Shu-YuL/AED-Smart-Alarm/Firmware/Base_Station/main/HD44780.c

#include <driver/i2c.h>
#include <esp_log.h>
#include <freertos/FreeRTOS.h>
#include <freertos/task.h>
#include <stdio.h>
#include "sdkconfig.h"
#include "rom/ets_sys.h"
#include <esp_log.h>
#include <string.h>

// LCD module defines
#define LCD_LINEONE             0x00        // start of line 1
#define LCD_LINETWO             0x40        // start of line 2
#define LCD_LINETHREE           0x14        // start of line 3
#define LCD_LINEFOUR            0x54        // start of line 4

#define LCD_BACKLIGHT           0x08
#define LCD_ENABLE              0x04               
#define LCD_COMMAND             0x00
#define LCD_WRITE               0x01

#define LCD_SET_DDRAM_ADDR      0x80
#define LCD_READ_BF             0x40

// LCD instructions
#define LCD_CLEAR               0x01        // replace all characters with ASCII 'space'
#define LCD_HOME                0x02        // return cursor to first position on first line
#define LCD_ENTRY_MODE          0x06        // shift cursor from left to right on read/write
#define LCD_DISPLAY_OFF         0x08        // turn display off
#define LCD_DISPLAY_ON          0x0C        // display on, cursor off, don't blink character
#define LCD_FUNCTION_RESET      0x30        // reset the LCD
#define LCD_FUNCTION_SET_4BIT   0x28        // 4-bit data, 2-line display, 5 x 7 font
#define LCD_SET_CURSOR          0x80        // set cursor position

// Pin mappings
// P0 -> RS
// P1 -> RW
// P2 -> E
// P3 -> Backlight
// P4 -> D4
// P5 -> D5
// P6 -> D6
// P7 -> D7

static char tag[] = "LCD Driver";
static uint8_t LCD_addr;
static uint8_t SDA_pin;
static uint8_t SCL_pin;
static uint8_t LCD_cols;
static uint8_t LCD_rows;

static void LCD_writeNibble(uint8_t nibble, uint8_t mode);
static void LCD_writeByte(uint8_t data, uint8_t mode);
static void LCD_pulseEnable(uint8_t nibble);


/*------------------------------------------
Function Name: I2C_init()
Description: Intiializes I2C on the the desired pins given by the macros SDA_pin, SCL_pin.
Input: N/A
Output: error code of type esp_err_t
Variables Affected: N/A
-------------------------------------------*/
static esp_err_t I2C_init(void)
{
    i2c_config_t conf = {
        .mode = I2C_MODE_MASTER,
        .sda_io_num = SDA_pin,
        .scl_io_num = SCL_pin,
        .sda_pullup_en = GPIO_PULLUP_ENABLE,
        .scl_pullup_en = GPIO_PULLUP_ENABLE,
        .master.clk_speed = 100000
    };
	i2c_param_config(I2C_NUM_0, &conf);
	i2c_driver_install(I2C_NUM_0, I2C_MODE_MASTER, 0, 0, 0);
    return ESP_OK;
}


/*------------------------------------------
Function Name: LCD_init()
Description: Initializes the LCD screen, clears the screen and setups the LCD to begin printing. 
Inputs: addr, dataPin, clockPin, cols, rows
Output: N/A
Variables Affected: N/A
-------------------------------------------*/
void LCD_init(uint8_t addr, uint8_t dataPin, uint8_t clockPin, uint8_t cols, uint8_t rows)
{
    LCD_addr = addr;
    SDA_pin = dataPin;
    SCL_pin = clockPin;
    LCD_cols = cols;
    LCD_rows = rows;
    I2C_init();
    vTaskDelay(100 / portTICK_PERIOD_MS);                                 // Initial 40 mSec delay

    // Reset the LCD controller
    LCD_writeNibble(LCD_FUNCTION_RESET, LCD_COMMAND);                   // First part of reset sequence
    vTaskDelay(10 / portTICK_PERIOD_MS);                                  // 4.1 mS delay (min)
    LCD_writeNibble(LCD_FUNCTION_RESET, LCD_COMMAND);                   // second part of reset sequence
    ets_delay_us(200);                                                  // 100 uS delay (min)
    LCD_writeNibble(LCD_FUNCTION_RESET, LCD_COMMAND);                   // Third time's a charm
    LCD_writeNibble(LCD_FUNCTION_SET_4BIT, LCD_COMMAND);                // Activate 4-bit mode
    ets_delay_us(80);                                                   // 40 uS delay (min)

    // --- Busy flag now available ---
    // Function Set instruction
    LCD_writeByte(LCD_FUNCTION_SET_4BIT, LCD_COMMAND);                  // Set mode, lines, and font
    ets_delay_us(80); 

    // Clear Display instruction
    LCD_writeByte(LCD_CLEAR, LCD_COMMAND);                              // clear display RAM
    vTaskDelay(2 / portTICK_PERIOD_MS);                                   // Clearing memory takes a bit longer
    
    // Entry Mode Set instruction
    LCD_writeByte(LCD_ENTRY_MODE, LCD_COMMAND);                         // Set desired shift characteristics
    ets_delay_us(80); 

    LCD_writeByte(LCD_DISPLAY_ON, LCD_COMMAND);                         // Ensure LCD is set to on
}


/*------------------------------------------
Function Name: LCD_setCursor()
Description: Moves the cursor to the location (row,col) specified by the inputs row and col. 
             Call this function to print a character at a desired location.
Inputs: col, row
Output: N/A
Variables Affected: N/A
-------------------------------------------*/
void LCD_setCursor(uint8_t col, uint8_t row)
{
    if (row > LCD_rows - 1) {
        ESP_LOGE(tag, "Cannot write to row %d. Please select a row in the range (0, %d)", row, LCD_rows-1);
        row = LCD_rows - 1;
    }
    uint8_t row_offsets[] = {LCD_LINEONE, LCD_LINETWO, LCD_LINETHREE, LCD_LINEFOUR};
    LCD_writeByte(LCD_SET_DDRAM_ADDR | (col + row_offsets[row]), LCD_COMMAND);
}


/*------------------------------------------
Function Name: LCD_writeChar()
Description: Prints a single character on the LCD screen.
Input: c => ASCII character to print
Output: N/A
Variables Affected: N/A
-------------------------------------------*/
void LCD_writeChar(char c)
{
    LCD_writeByte(c, LCD_WRITE); // Write data to DDRAM
}


/*------------------------------------------
Function Name: LCD_writeStr()
Description: Prints a string of characters on the LCD screen.
Input: str => pointer to string to print.
Output: N/A
Variables Affected: N/A
-------------------------------------------*/
void LCD_writeStr(char* str)
{
    while (*str) {
        LCD_writeChar(*str++);
    }
}


/*------------------------------------------
Function Name: LCD_home()
Description: 
Input: N/A
Output: N/A
Variables Affected: N/A
-------------------------------------------*/
void LCD_home(void)
{
    LCD_writeByte(LCD_HOME, LCD_COMMAND);
    vTaskDelay(2 / portTICK_PERIOD_MS);   // This command takes a while to complete
}


/*------------------------------------------
Function Name: LCD_clearScreen()
Description: Completely clears the LCD screen. Waits 2s to allow screen to finish clearing.
Input: N/A
Output: N/A
Variables Affected: N/A
-------------------------------------------*/
void LCD_clearScreen(void)
{
    LCD_writeByte(LCD_CLEAR, LCD_COMMAND);
    vTaskDelay(2 / portTICK_PERIOD_MS);   // This command takes a while to complete
}


/*------------------------------------------
Function Name: LCD_writeNibble()
Description: Writes a nibble of data to the LCD controller via I2C.
Inputs: nibble => nibble of data to write to LCD
       mode
Output: N/A
Variables Affected: N/A
-------------------------------------------*/
static void LCD_writeNibble(uint8_t nibble, uint8_t mode)
{
    uint8_t data = (nibble & 0xF0) | mode | LCD_BACKLIGHT;
    i2c_cmd_handle_t cmd = i2c_cmd_link_create();
    ESP_ERROR_CHECK(i2c_master_start(cmd));
    ESP_ERROR_CHECK(i2c_master_write_byte(cmd, (LCD_addr << 1) | I2C_MASTER_WRITE, 1));
    ESP_ERROR_CHECK(i2c_master_write_byte(cmd, data, 1));
    ESP_ERROR_CHECK(i2c_master_stop(cmd));
    ESP_ERROR_CHECK(i2c_master_cmd_begin(I2C_NUM_0, cmd, 1000/portTICK_PERIOD_MS));
    i2c_cmd_link_delete(cmd);   

    LCD_pulseEnable(data); // Clock data into LCD
}


/*------------------------------------------
Function Name: LCD_writeByte()
Description: Writes a full byte of data to the LCD controller by writing the upper and lower nibble of data 
             as two transactions using LCD_writeNibble().
Inputs: data => byte of data to write to LCD
        mode
Output: N/A
Variables Affected: N/A
-------------------------------------------*/
static void LCD_writeByte(uint8_t data, uint8_t mode)
{
    LCD_writeNibble(data & 0xF0, mode);
    LCD_writeNibble((data << 4) & 0xF0, mode);
}


/*------------------------------------------
Function Name: LCD_pulseEnable()
Description: 
Input: data
Output: N/A
Variables Affected: N/A
-------------------------------------------*/
static void LCD_pulseEnable(uint8_t data)
{
    i2c_cmd_handle_t cmd = i2c_cmd_link_create();
    ESP_ERROR_CHECK(i2c_master_start(cmd));
    ESP_ERROR_CHECK(i2c_master_write_byte(cmd, (LCD_addr << 1) | I2C_MASTER_WRITE, 1));
    ESP_ERROR_CHECK(i2c_master_write_byte(cmd, data | LCD_ENABLE, 1));
    ESP_ERROR_CHECK(i2c_master_stop(cmd));
    ESP_ERROR_CHECK(i2c_master_cmd_begin(I2C_NUM_0, cmd, 1000/portTICK_PERIOD_MS));
    i2c_cmd_link_delete(cmd);  
    ets_delay_us(1);

    cmd = i2c_cmd_link_create();
    ESP_ERROR_CHECK(i2c_master_start(cmd));
    ESP_ERROR_CHECK(i2c_master_write_byte(cmd, (LCD_addr << 1) | I2C_MASTER_WRITE, 1));
    ESP_ERROR_CHECK(i2c_master_write_byte(cmd, (data & ~LCD_ENABLE), 1));
    ESP_ERROR_CHECK(i2c_master_stop(cmd));
    ESP_ERROR_CHECK(i2c_master_cmd_begin(I2C_NUM_0, cmd, 1000/portTICK_PERIOD_MS));
    i2c_cmd_link_delete(cmd);
    ets_delay_us(500);
}


/*------------------------------------------
Function Name: ()
Description: This function will print any characters to the LCD display. The first argument is the x position,
             the second argument is the y position, the third argument is whatever you wanna write to the OLED display,
             the fourth argument is an integer (if no integer -> write NA), the last argument is a string of characters
             (if no string -> write NA). Please include " " for the third argument.
Inputs: x_position, y_position, txt, var, message
Output: N/A
Variables Affected: N/A
-------------------------------------------*/
void LCD_printf(uint8_t x_position, uint8_t y_position, char txt[], uint8_t var, char message[])
{
    char txtBuf[8];
    uint8_t num_buff;
    if(var)
    {
        LCD_setCursor(y_position, x_position);
        LCD_writeStr(txt);
        num_buff = strlen(txt);
        sprintf(txtBuf, "%d", var);
        LCD_setCursor(++num_buff, x_position);
        LCD_writeStr(txtBuf);
    }
    else if(message)
    {
        LCD_setCursor(y_position, x_position);
        LCD_writeStr(txt);
        num_buff = strlen(txt);
        LCD_setCursor(++num_buff, x_position);
        LCD_writeStr(message);
    }
    else
    {
        LCD_setCursor(y_position, x_position);
        LCD_writeStr(txt);
    }
}
