Shu-YuL/AED-Smart-Alarm/Firmware/Monitoring_Device/main/wifi_functions.c

#include "wifi_include.h"

static const char *TAG = "WIFI";

/* Description: This file contains functions specifically for establishing a WiFi connection to a standard, non-WPA2 WiFi network like DevNet or a home network*/

#ifdef HOME

/* FreeRTOS event group to signal when wifi is connected*/
static EventGroupHandle_t s_wifi_event_group;

static int s_retry_num = 0;

/*------------------------------------------
Function Name: event_handler()
Description: FreeRTOS event handler to indicate when WiFi is connected. 
             Retries to connect to a WiFi access point upto WIFI_MAX_TRIES, and prints IP address of network when successful.
Input: arg, event_base, event_id, event_data
Output: N/A
Variables Affected: s_retry_num, s_wifi_event_group
-------------------------------------------*/
static void event_handler(void *arg, esp_event_base_t event_base,
                          int32_t event_id, void *event_data)
{
    if (event_base == WIFI_EVENT && event_id == WIFI_EVENT_STA_START)
    {
        esp_wifi_connect();
    }
    else if (event_base == WIFI_EVENT && event_id == WIFI_EVENT_STA_DISCONNECTED)
    {
        if (s_retry_num < WIFI_MAX_TRIES)
        {
            esp_wifi_connect();
            s_retry_num++;
            ESP_LOGI(TAG, "retry to connect to the AP");
        }
        else
        {
            xEventGroupSetBits(s_wifi_event_group, WIFI_FAIL_BIT);
        }
        ESP_LOGI(TAG, "connect to the AP fail");
    }
    else if (event_base == IP_EVENT && event_id == IP_EVENT_STA_GOT_IP)
    {
        ip_event_got_ip_t *event = (ip_event_got_ip_t *)event_data;
        ESP_LOGI(TAG, "got ip:" IPSTR, IP2STR(&event->ip_info.ip));
        s_retry_num = 0;
        xEventGroupSetBits(s_wifi_event_group, WIFI_CONNECTED_BIT);
    }
}

/*------------------------------------------
Function Name: connect_wifi()
Description: Sets up ESP32 as a WiFi station and configures parameters such as ssid and password, and starts WiFi.
             Connects to a regular WiFi network like a home network or DevNet and indicates connection status.
Input: N/A
Output: N/A
Variables Affected: N/A
-------------------------------------------*/
void connect_wifi(void)
{
    s_wifi_event_group = xEventGroupCreate();

    ESP_ERROR_CHECK(esp_netif_init());

    ESP_ERROR_CHECK(esp_event_loop_create_default());
    esp_netif_create_default_wifi_sta();

    wifi_init_config_t cfg = WIFI_INIT_CONFIG_DEFAULT();
    ESP_ERROR_CHECK(esp_wifi_init(&cfg));

    esp_event_handler_instance_t instance_any_id;
    esp_event_handler_instance_t instance_got_ip;
    ESP_ERROR_CHECK(esp_event_handler_instance_register(WIFI_EVENT,
                                                        ESP_EVENT_ANY_ID,
                                                        &event_handler,
                                                        NULL,
                                                        &instance_any_id));
    ESP_ERROR_CHECK(esp_event_handler_instance_register(IP_EVENT,
                                                        IP_EVENT_STA_GOT_IP,
                                                        &event_handler,
                                                        NULL,
                                                        &instance_got_ip));

    wifi_config_t wifi_config = {
        .sta = {
            .ssid = WIFI_SSID,
            .password = WIFI_PASSWORD,
            /* Setting a password implies station will connect to all security modes including WEP/WPA.
             * However these modes are deprecated and not advisable to be used. Incase your Access point
             * doesn't support WPA2, these mode can be enabled by commenting below line */
            .threshold.authmode = WIFI_AUTH_WPA2_PSK,
        },
    };
    ESP_ERROR_CHECK(esp_wifi_set_mode(WIFI_MODE_STA));
    ESP_ERROR_CHECK(esp_wifi_set_config(WIFI_IF_STA, &wifi_config));
    ESP_ERROR_CHECK(esp_wifi_start());

    ESP_LOGI(TAG, "wifi_init_sta finished.");

    /* Waiting until either the connection is established (WIFI_CONNECTED_BIT) or connection failed for the maximum
     * number of re-tries (WIFI_FAIL_BIT). The bits are set by event_handler() (see above) */
    EventBits_t bits = xEventGroupWaitBits(s_wifi_event_group,
                                           WIFI_CONNECTED_BIT | WIFI_FAIL_BIT,
                                           pdFALSE,
                                           pdFALSE,
                                           portMAX_DELAY);

    /* xEventGroupWaitBits() returns the bits before the call returned, hence we can test which event actually
     * happened. */
    if (bits & WIFI_CONNECTED_BIT)
    {
        ESP_LOGI(TAG, "connected to ap SSID:%s password:%s",
                 WIFI_SSID, WIFI_PASSWORD);
    }
    else if (bits & WIFI_FAIL_BIT)
    {
        ESP_LOGI(TAG, "Failed to connect to SSID:%s, password:%s",
                 WIFI_SSID, WIFI_PASSWORD);
    }
    else
    {
        ESP_LOGE(TAG, "UNEXPECTED EVENT");
    }
    vEventGroupDelete(s_wifi_event_group);
}

#endif
