Shu-YuL/AED-Smart-Alarm/Firmware/Monitoring_Device_CAM/main/camera_functions.c

#include "camera_include.h"

/* Defining TAG name for debugging */
static const char *TAG = "esp32-cam Webserver";
/* Defining static global variables */
static const char* _STREAM_CONTENT_TYPE = "multipart/x-mixed-replace;boundary=" PART_BOUNDARY;
static const char* _STREAM_BOUNDARY = "\r\n--" PART_BOUNDARY "\r\n";
static const char* _STREAM_PART = "Content-Type: image/jpeg\r\nContent-Length: %u\r\n\r\n";

/* -----------------------------------------------------------------------------------------
 * Subroutine Name: init_camera
 * Description: This function initializes a number of fields that specify the configuration
                for the ESP32-CAM.
 * Input: void
 * Output: - esp_err_t value indicating the status of the initialization
           - ESP-OK -> no errors occurred
 * Registers Affected: N/A
 ----------------------------------------------------------------------------------------- */
esp_err_t init_camera(void)
{
    camera_config_t camera_config = {
        .pin_pwdn  = CAM_PIN_PWDN,
        .pin_reset = CAM_PIN_RESET,
        .pin_xclk = CAM_PIN_XCLK,
        .pin_sccb_sda = CAM_PIN_SIOD,
        .pin_sccb_scl = CAM_PIN_SIOC,

        .pin_d7 = CAM_PIN_D7,
        .pin_d6 = CAM_PIN_D6,
        .pin_d5 = CAM_PIN_D5,
        .pin_d4 = CAM_PIN_D4,
        .pin_d3 = CAM_PIN_D3,
        .pin_d2 = CAM_PIN_D2,
        .pin_d1 = CAM_PIN_D1,
        .pin_d0 = CAM_PIN_D0,
        .pin_vsync = CAM_PIN_VSYNC,
        .pin_href = CAM_PIN_HREF,
        .pin_pclk = CAM_PIN_PCLK,

        .xclk_freq_hz = CONFIG_XCLK_FREQ,
        .ledc_timer = LEDC_TIMER_0,
        .ledc_channel = LEDC_CHANNEL_0,

        .pixel_format = PIXFORMAT_JPEG,
        .frame_size = FRAMESIZE_VGA,

        .jpeg_quality = 10,
        .fb_count = 1,
        .grab_mode = CAMERA_GRAB_WHEN_EMPTY};//CAMERA_GRAB_LATEST. Sets when buffers should be filled
    esp_err_t err = esp_camera_init(&camera_config);

    /* check if errors */
    if (err != ESP_OK)
    {
        return err;
    }
    return ESP_OK; /* Good to go */
}

/* -----------------------------------------------------------------------------------------
 * Subroutine Name: jpg_stream_httpd_handler
 * Description: This function is called to handle GET requests on the root URI of the HTTP
                server. It streams whatever the camera is capturing and sends the buffer
                containing JPEG images and publish content on the HTTP server.
 * Input: HTTP request type
 * Output: function returns the error response
 * Registers Affected: N/A
 ----------------------------------------------------------------------------------------- */
esp_err_t jpg_stream_httpd_handler(httpd_req_t *req){
    camera_fb_t * fb = NULL;
    esp_err_t res = ESP_OK;
    size_t _jpg_buf_len;
    uint8_t * _jpg_buf;
    char * part_buf[64];
    static int64_t last_frame = 0;
    
    if(!last_frame) {
        last_frame = esp_timer_get_time();
    }

    res = httpd_resp_set_type(req, _STREAM_CONTENT_TYPE);
    if(res != ESP_OK){
        return res;
    }

    /* Loop that captures frames from the camera continuously */
    while(true){
        fb = esp_camera_fb_get();
        if (!fb) {
            ESP_LOGE(TAG, "Camera capture failed");
            res = ESP_FAIL;
            break;
        }
        if(fb->format != PIXFORMAT_JPEG){
            bool jpeg_converted = frame2jpg(fb, 80, &_jpg_buf, &_jpg_buf_len);
            if(!jpeg_converted){
                ESP_LOGE(TAG, "JPEG compression failed");
                esp_camera_fb_return(fb);
                res = ESP_FAIL;
            }
        } else {
            _jpg_buf_len = fb->len;
            _jpg_buf = fb->buf;
        }

        if(res == ESP_OK){
            res = httpd_resp_send_chunk(req, _STREAM_BOUNDARY, strlen(_STREAM_BOUNDARY));
        }
        if(res == ESP_OK){
            size_t hlen = snprintf((char *)part_buf, 64, _STREAM_PART, _jpg_buf_len);

            res = httpd_resp_send_chunk(req, (const char *)part_buf, hlen);
        }
        if(res == ESP_OK){
            res = httpd_resp_send_chunk(req, (const char *)_jpg_buf, _jpg_buf_len);
        }
        if(fb->format != PIXFORMAT_JPEG){
            free(_jpg_buf);
        }
        esp_camera_fb_return(fb);
        if(res != ESP_OK){
            break;
        }
        int64_t fr_end = esp_timer_get_time();
        int64_t frame_time = fr_end - last_frame;
        last_frame = fr_end;
        frame_time /= 1000;
        ESP_LOGI(TAG, "MJPG: %uKB %ums (%.1ffps)",
            (uint32_t)(_jpg_buf_len/1024),
            (uint32_t)frame_time, 1000.0 / (uint32_t)frame_time);
    }

    last_frame = 0;
    return res;
}

/* Specify behavior when client request GET on the root URL */
httpd_uri_t uri_get = {
    .uri = "/",
    .method = HTTP_GET,
    .handler = jpg_stream_httpd_handler,
    .user_ctx = NULL
};

/* -----------------------------------------------------------------------------------------
 * Subroutine Name: setup_server
 * Description: This function sets up an HTTP server to get request on the URI root. When GET
                request is received, the server follows the behavior specified above to 
                handel the request.
 * Input: void
 * Output: function returns error message
 * Registers Affected: N/A
 ----------------------------------------------------------------------------------------- */
httpd_handle_t setup_server(void)
{
    httpd_config_t config = HTTPD_DEFAULT_CONFIG();
    httpd_handle_t stream_httpd  = NULL;

    if (httpd_start(&stream_httpd , &config) == ESP_OK)
    {
        httpd_register_uri_handler(stream_httpd , &uri_get);
    }

    return stream_httpd;
}
