Shu-YuL/AED-Smart-Alarm/Firmware/Base_Station/main/HD44780.h

#pragma once

/* Includes */
#include <string.h>
#include <driver/i2c.h>
#include <esp_log.h>
#include <freertos/FreeRTOS.h>
#include <freertos/task.h>
#include <stdio.h>
#include "sdkconfig.h"
#include "HD44780.h"

/* Definitions */
#define LCD_ADDR 0x27
#define SDA_PIN  18
#define SCL_PIN  19
#define LCD_COLS 20
#define LCD_ROWS 4
#define NA 0

/* Function Prototypes */
void LCD_init(uint8_t addr, uint8_t dataPin, uint8_t clockPin, uint8_t cols, uint8_t rows);
void LCD_setCursor(uint8_t col, uint8_t row);
void LCD_home(void);
void LCD_clearScreen(void);
void LCD_writeChar(char c);
void LCD_writeStr(char* str); 
void LCD_DemoTask(void* param);
void LCD_printf(uint8_t x_position, uint8_t y_position, char txt[], uint8_t var, char message[]);
